irwintr/irwintr.github.io/IMG_20160906_150515.jpg

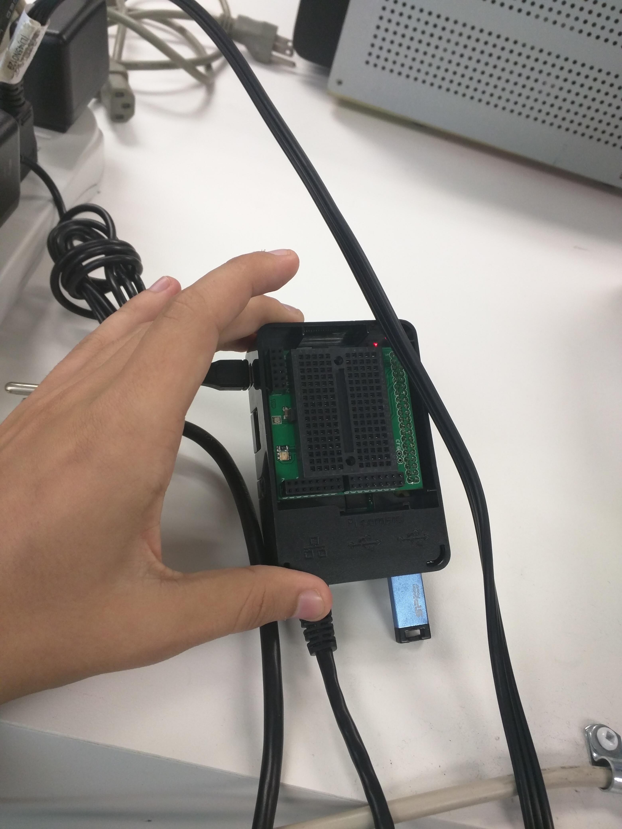
IMG_20160906_150515.jpg
