irwintr/irwintr.github.io/IMG_20161011_145405.jpg

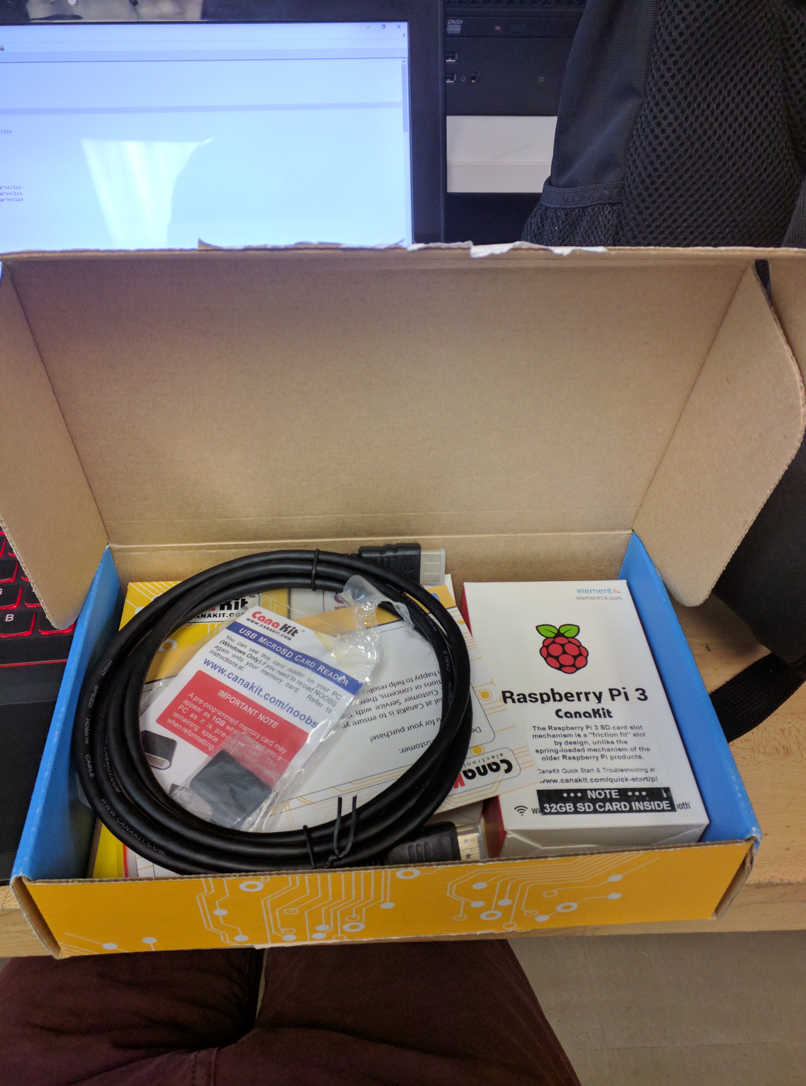
IMG_20161011_145405.jpg
